STRML/macbook-upright-cooler/cad/upright_v2/v12_validation/stl/coupon_collar.stl

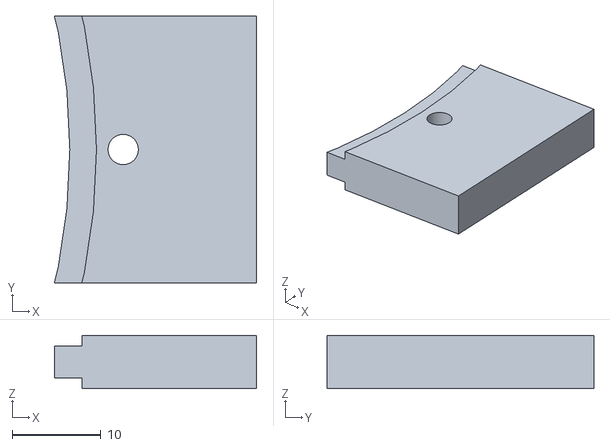
[picture p20: CAD file, 2026-09-15]
cad/upright_v2/v12_validation/stl/coupon_collar.stl
22.7 x 30.0 x 6.00
