STRML/macbook-upright-cooler/cad/upright_v2/stl/foot.stl

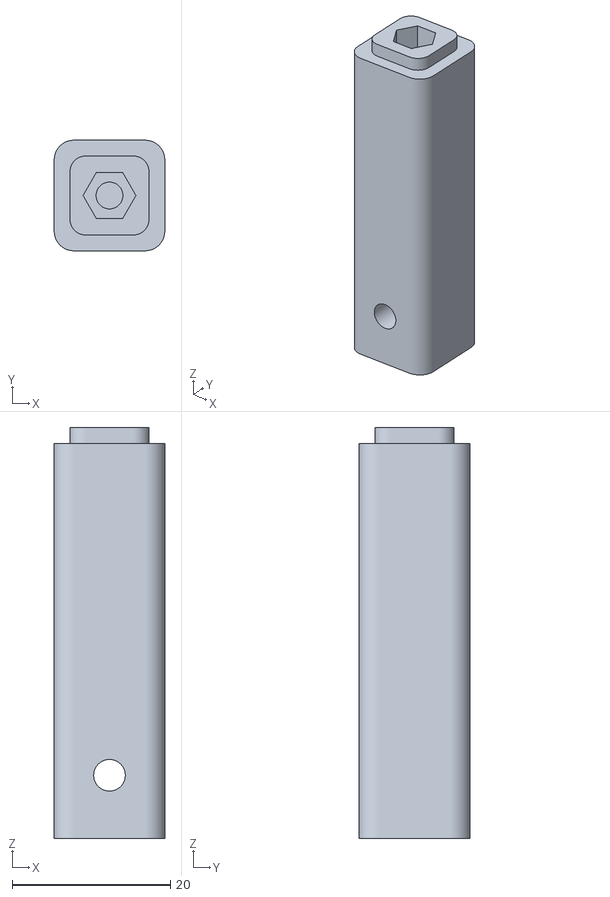
[picture p21: CAD file, 2026-09-15]
cad/upright_v2/stl/foot.stl
14.0 x 14.0 x 52.0
