STRML/macbook-upright-cooler/cad/upright_v2/v12_validation/stl/gauge_nw.stl

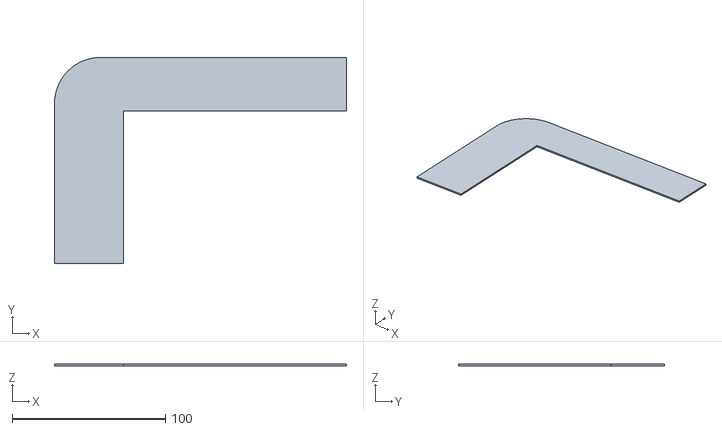
[picture p22: CAD file, 2026-09-15]
cad/upright_v2/v12_validation/stl/gauge_nw.stl
190.4 x 134.4 x 1.20
