STRML/macbook-upright-cooler/cad/upright_v2/v12_validation/stl/collar.stl

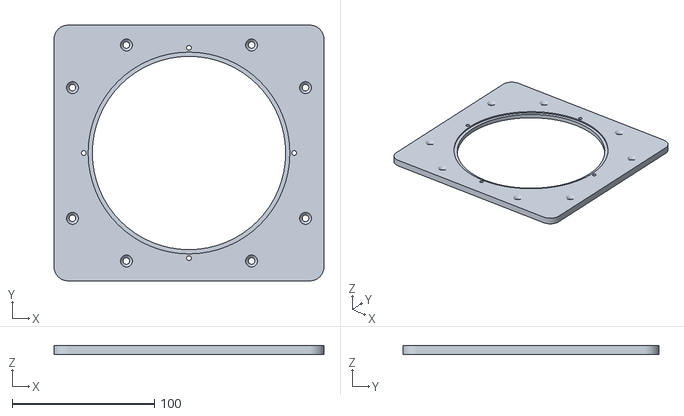
[picture p23: CAD file, 2026-09-15]
cad/upright_v2/v12_validation/stl/collar.stl
190.0 x 180.0 x 6.00
