STRML/macbook-upright-cooler/cad/upright_v2/v12_validation/stl/bridge.stl

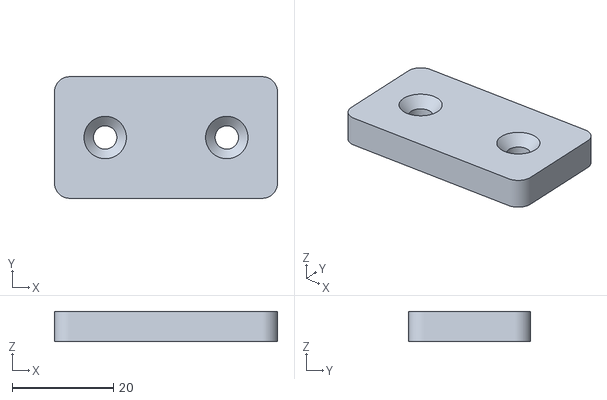
[picture p24: CAD file, 2026-09-15]
cad/upright_v2/v12_validation/stl/bridge.stl
44.0 x 24.0 x 6.00
