STRML/macbook-upright-cooler/cad/upright_v2/v12_validation/stl/coupon_se.stl

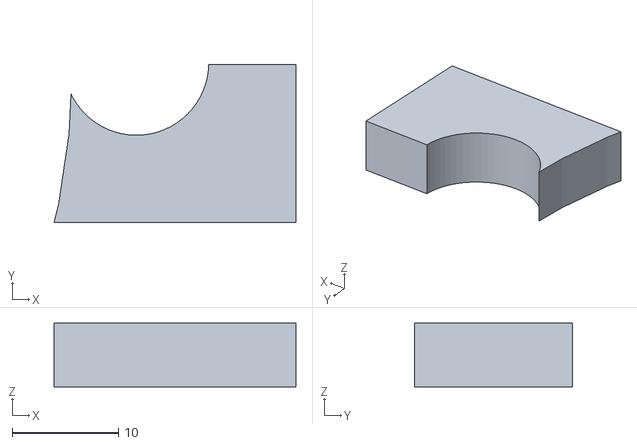
[picture p25: CAD file, 2026-09-15]
cad/upright_v2/v12_validation/stl/coupon_se.stl
22.7 x 14.8 x 6.00
